7Ayush-cyber/Robotics_Kriti_25/compactor_wall_1.SLDPRT

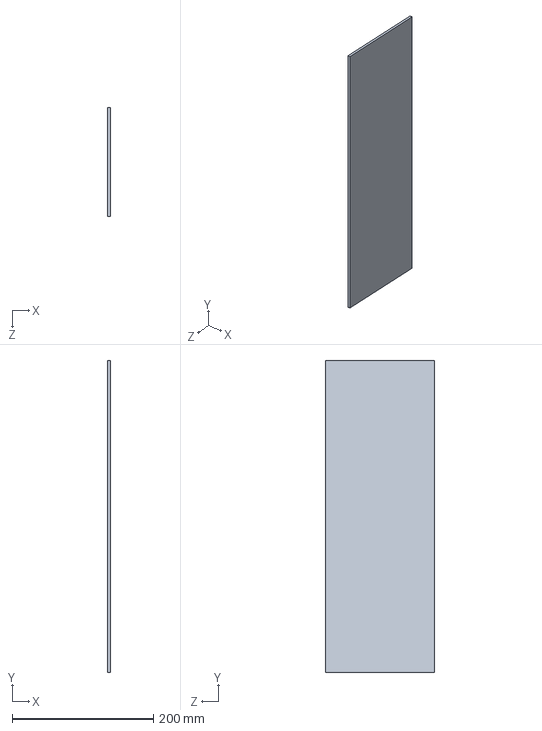
[picture p23: CAD file, 2025-03-05]
compactor_wall_1.SLDPRT
4.00 x 442.0 x 154.0 mm
