7Ayush-cyber/Robotics_Kriti_25/plastic_holder_side_1.SLDPRT

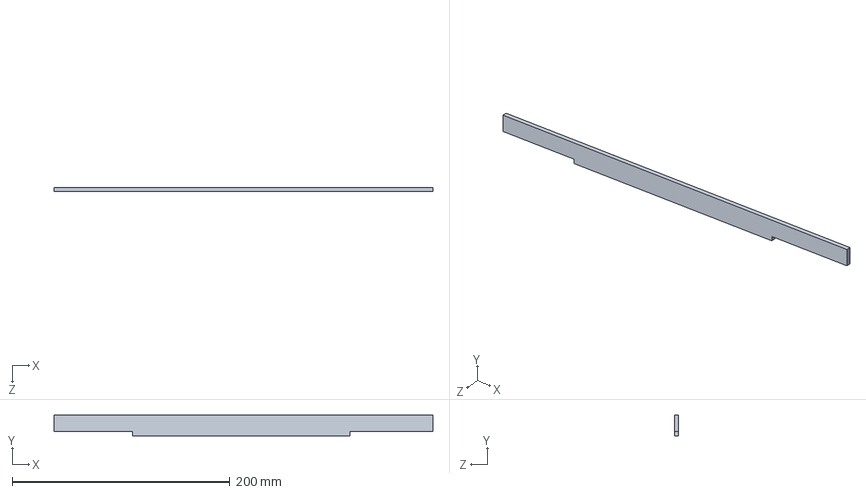
[picture p24: CAD file, 2025-03-05]
plastic_holder_side_1.SLDPRT
348.0 x 19.0 x 4.00 mm
