7Ayush-cyber/Robotics_Kriti_25/motor_side.SLDPRT

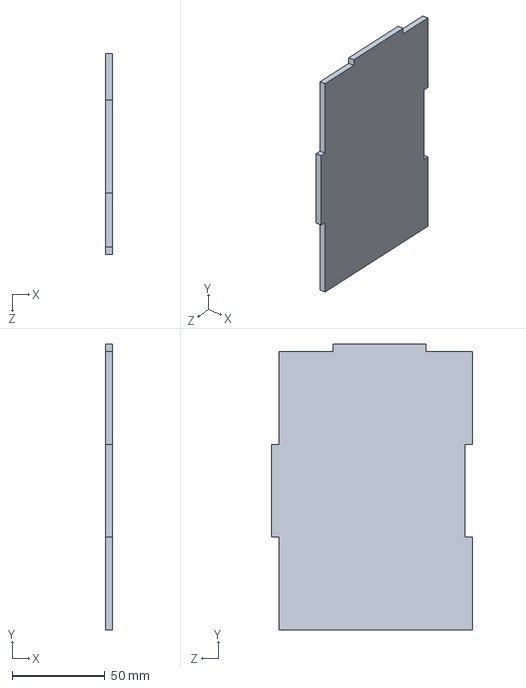
[picture p25: CAD file, 2025-03-05]
motor_side.SLDPRT
4.00 x 154.0 x 108.0 mm
