7Ayush-cyber/Robotics_Kriti_25/lid.SLDPRT

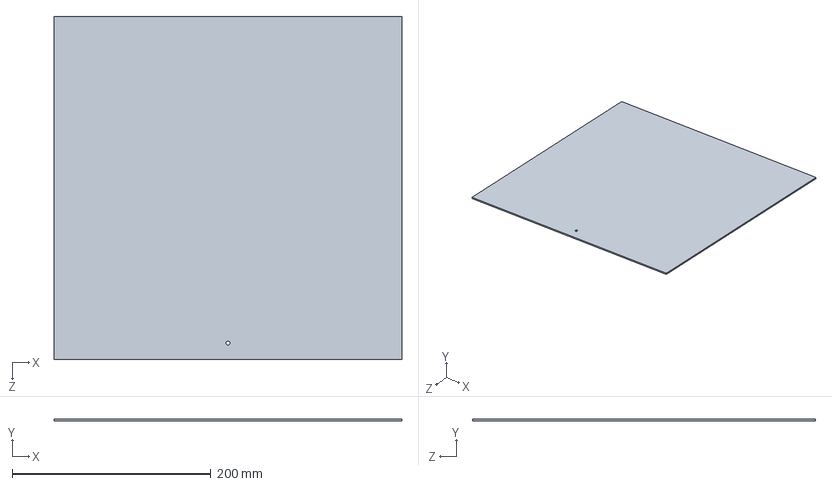
[picture p26: CAD file, 2025-03-05]
lid.SLDPRT
350.0 x 2.00 x 345.0 mm
