7Ayush-cyber/Robotics_Kriti_25/sealing_mount.SLDPRT

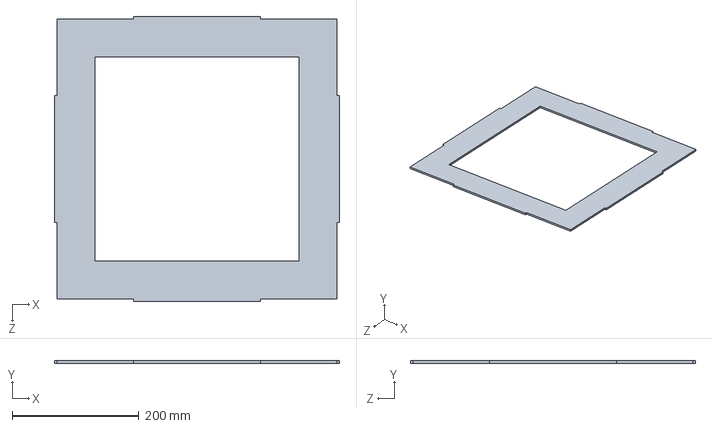
[picture p27: CAD file, 2025-03-05]
sealing_mount.SLDPRT
450.0 x 4.00 x 450.0 mm
