7Ayush-cyber/Robotics_Kriti_25/plastic_base.SLDPRT

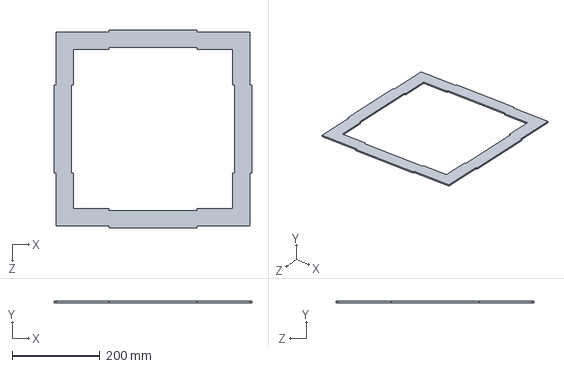
[picture p28: CAD file, 2025-03-05]
plastic_base.SLDPRT
450.0 x 4.00 x 450.0 mm
