7Ayush-cyber/Robotics_Kriti_25/storage_base.SLDPRT

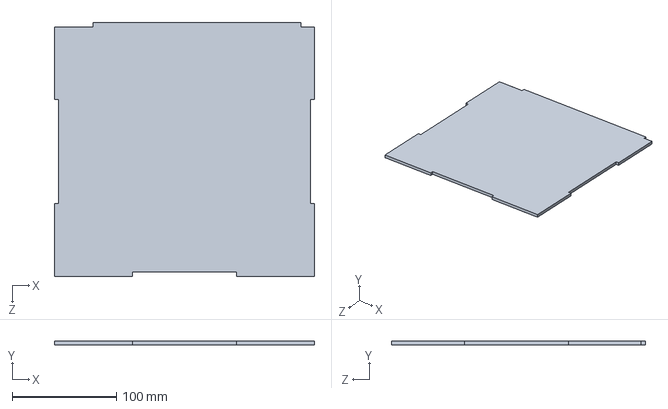
[picture p29: CAD file, 2025-03-05]
storage_base.SLDPRT
250.0 x 4.00 x 244.0 mm
