7Ayush-cyber/Robotics_Kriti_25/Motor_front.SLDPRT

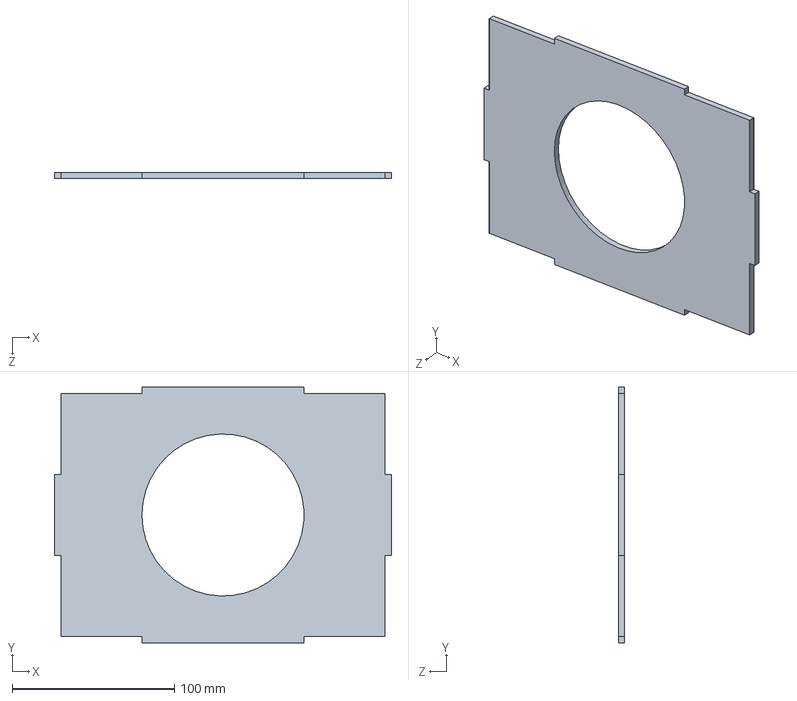
[picture p30: CAD file, 2025-03-05]
Motor_front.SLDPRT
208.0 x 158.0 x 4.00 mm
