7Ayush-cyber/Robotics_Kriti_25/motor_base.SLDPRT

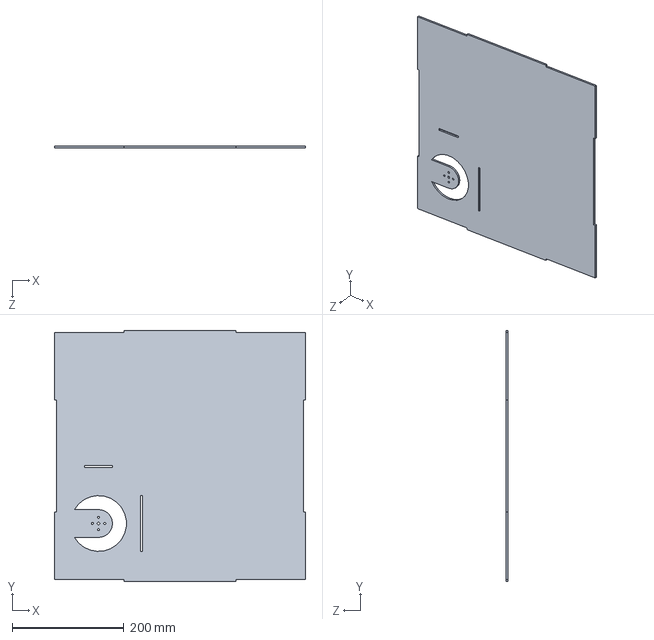
[picture p31: CAD file, 2025-03-05]
motor_base.SLDPRT
450.0 x 450.0 x 4.00 mm
