7Ayush-cyber/Robotics_Kriti_25/motor_roof.SLDPRT

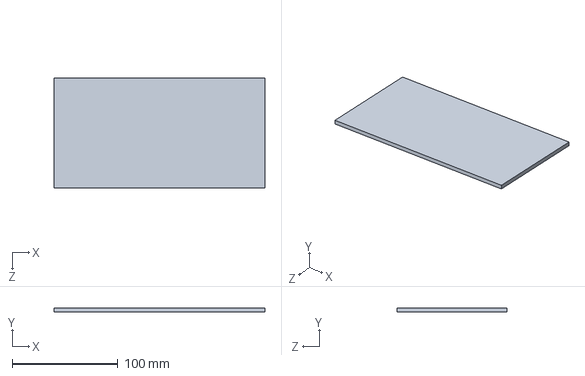
[picture p32: CAD file, 2025-03-05]
motor_roof.SLDPRT
200.0 x 4.00 x 104.0 mm
