7Ayush-cyber/Robotics_Kriti_25/plastic_wrapper.SLDPRT

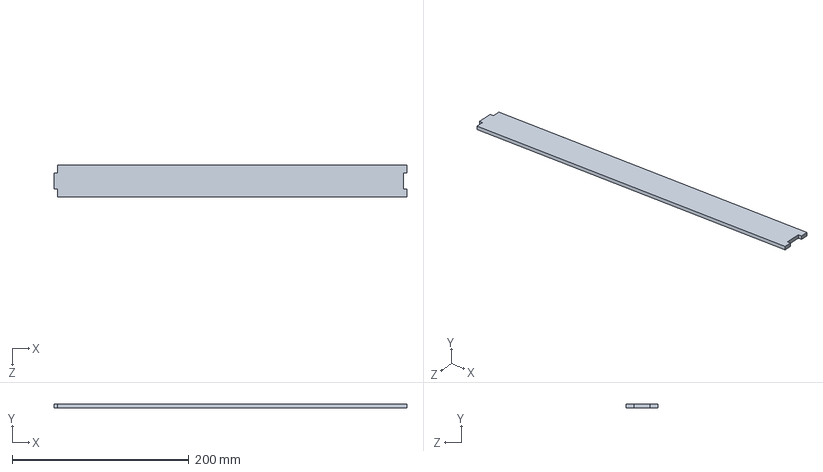
[picture p33: CAD file, 2025-03-05]
plastic_wrapper.SLDPRT
400.0 x 4.00 x 36.0 mm
