7Ayush-cyber/Robotics_Kriti_25/storage_front.SLDPRT

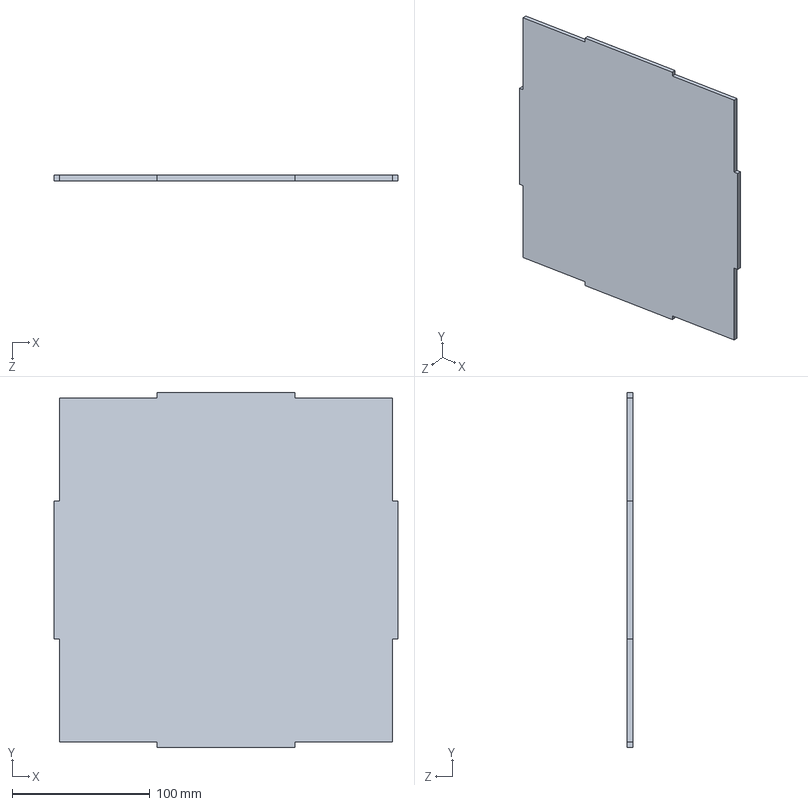
[picture p34: CAD file, 2025-03-05]
storage_front.SLDPRT
250.0 x 258.0 x 4.00 mm
