7Ayush-cyber/Robotics_Kriti_25/side_wall_2.SLDPRT

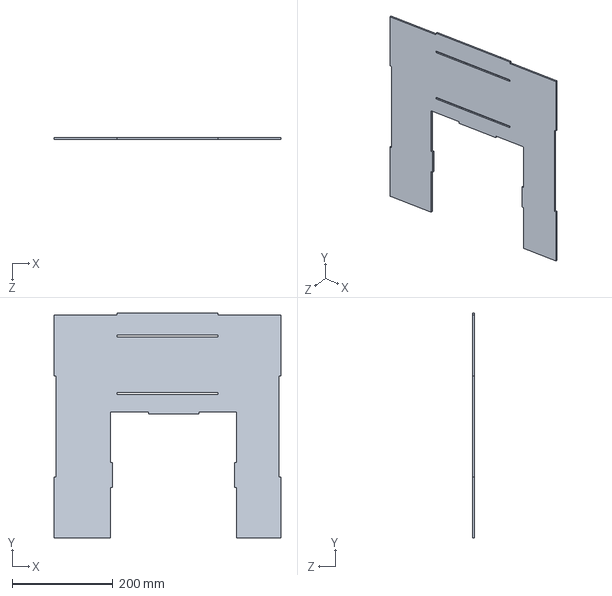
[picture p35: CAD file, 2025-03-05]
side_wall_2.SLDPRT
450.0 x 446.0 x 4.00 mm
